svenpetersen1965/1541-parallel-adapter-SpeedDOS/1541_VIA_Parallel_Adapter_lowP/Rev. 0/pictures/5152_-_pin_socket_alignment.JPG

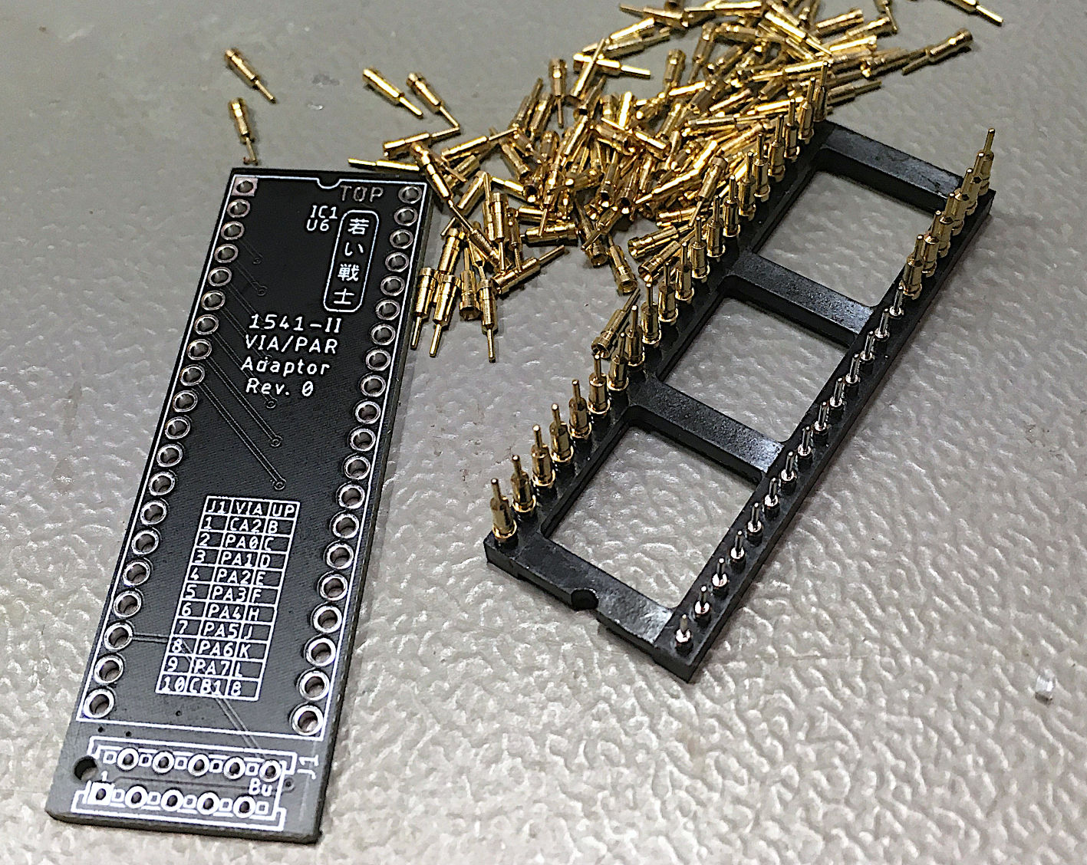
1541_VIA_Parallel_Adapter_lowP/Rev. 0/pictures/5152_-_pin_socket_alignment.JPG
