svenpetersen1965/1541-parallel-adapter-SpeedDOS/1541_VIA_Parallel_Adapter_lowP/Rev. 0/pictures/5259_-_1541-II_connectors.JPG

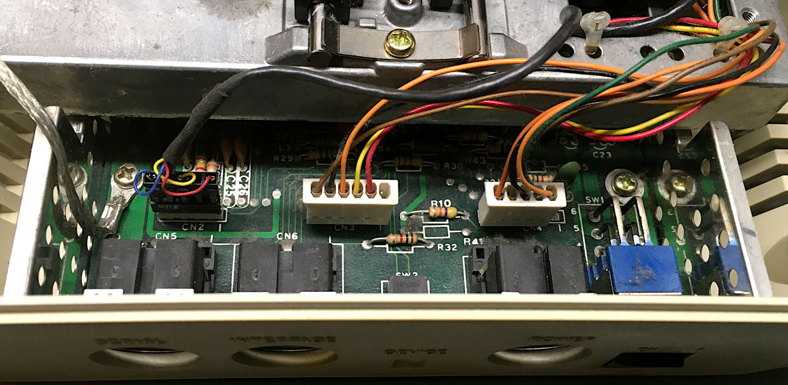
1541_VIA_Parallel_Adapter_lowP/Rev. 0/pictures/5259_-_1541-II_connectors.JPG
