svenpetersen1965/1541-parallel-adapter-SpeedDOS/UserP_Parallel_Adapter/case/Label/UserP_Parallel_Label.png

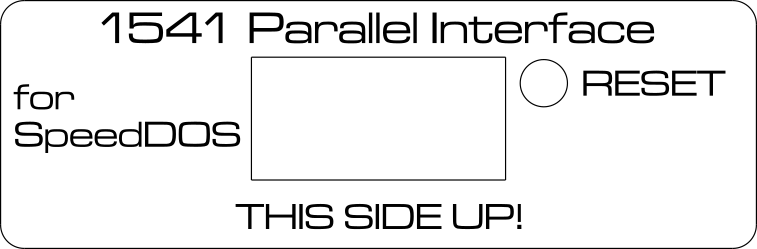
UserP_Parallel_Adapter/case/Label/UserP_Parallel_Label.png
