svenpetersen1965/1541-parallel-adapter-SpeedDOS/UserP_Parallel_Adapter/Rev. 0/pictures/5251_-_UP-Adapter.JPG

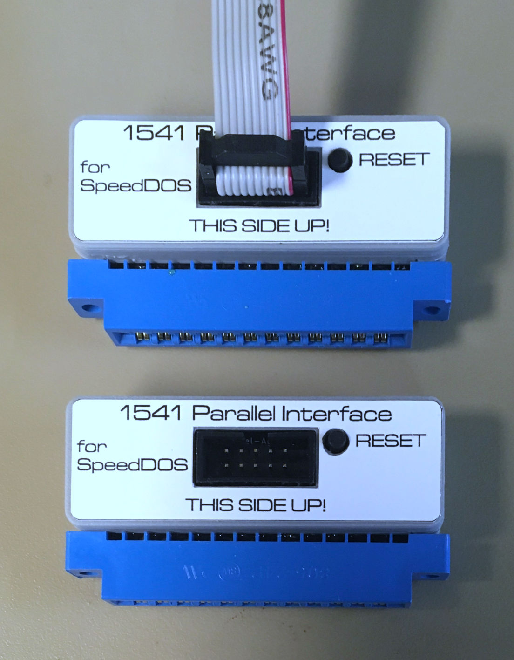
UserP_Parallel_Adapter/Rev. 0/pictures/5251_-_UP-Adapter.JPG
